fablab-fb16/pcb_workshop_christmas_2023/documentation/images/back.jpg

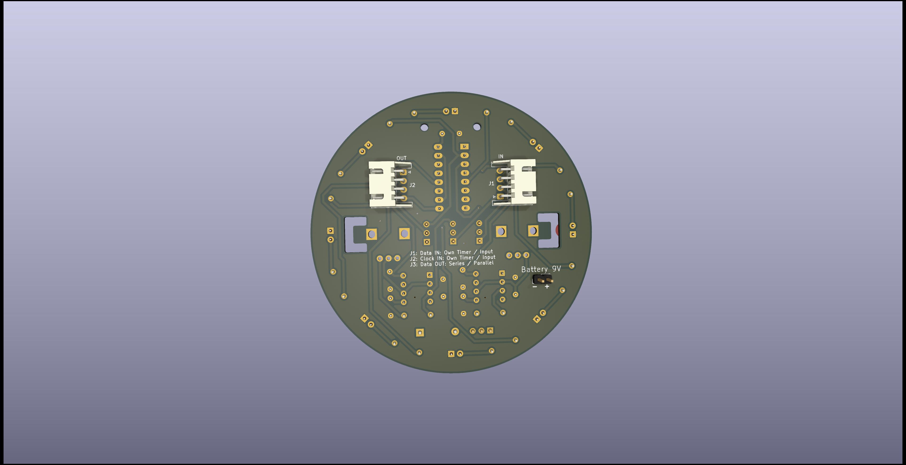
documentation/images/back.jpg
