fablab-fb16/pcb_workshop_christmas_2023/notebooks/lin_vs_log.png

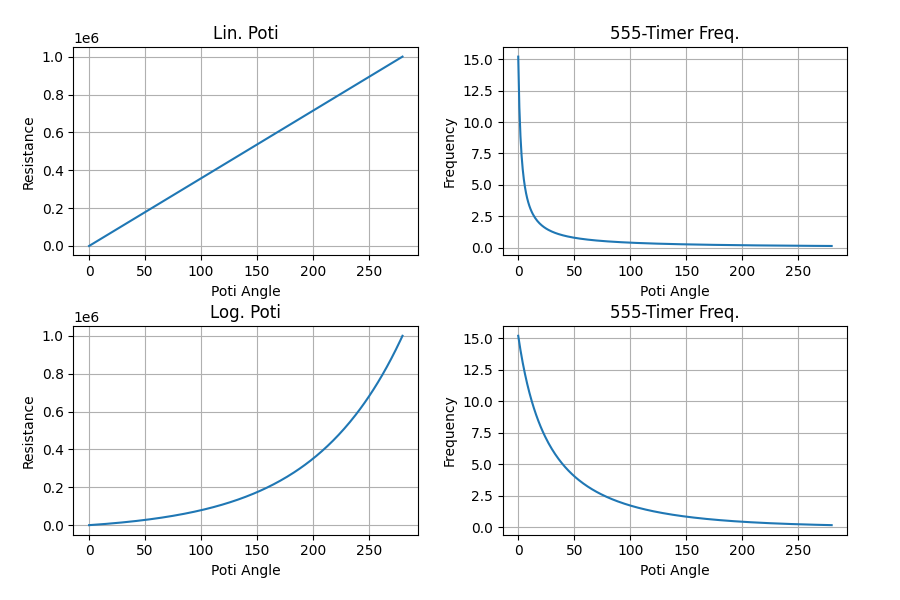
notebooks/lin_vs_log.png
